caio-alcantara/Inclinometro-Bristol/src/Inc-Bristol-Fisico-0003/include/SensorManager.h

#pragma once
#include <MPU9250.h>
#include <Wire.h>

class SensorManager {
    public:
        struct SensorData {
            struct { float x, y, z; } accel, gyro, mag;
            float yaw, pitch, roll;
        };

        SensorManager(MPU9250& sensor);
        bool initialize();
        void calibrateAccelGyro();
        bool update();
        SensorData getData() const;

    private:
        MPU9250& mpu;
};
